IsaBellaBortoleto/AirDrums/Fotos/WhatsApp Image 2025-02-23 at 17.46.49 (1).jpeg

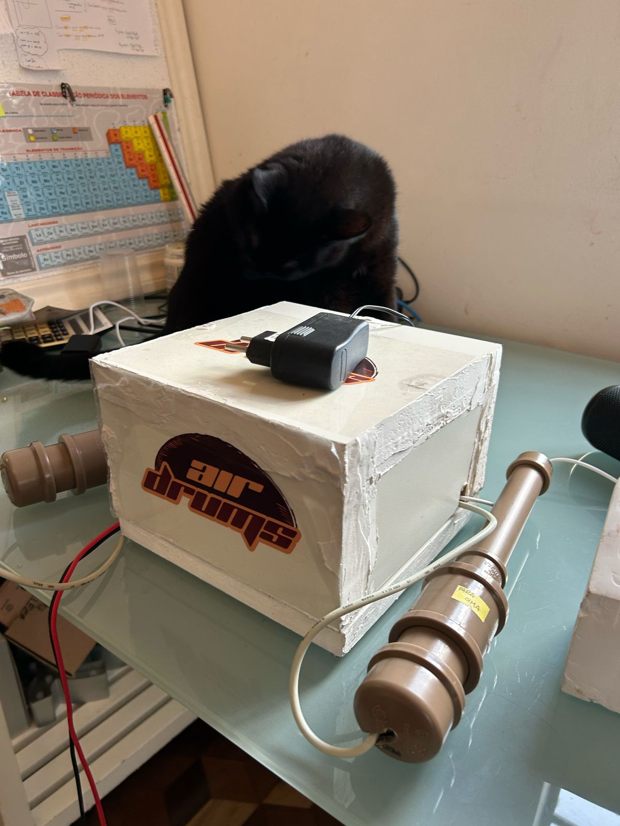
Fotos/WhatsApp Image 2025-02-23 at 17.46.49 (1).jpeg
