IsaBellaBortoleto/AirDrums/Vetores/diagrama_pretoebranco.png

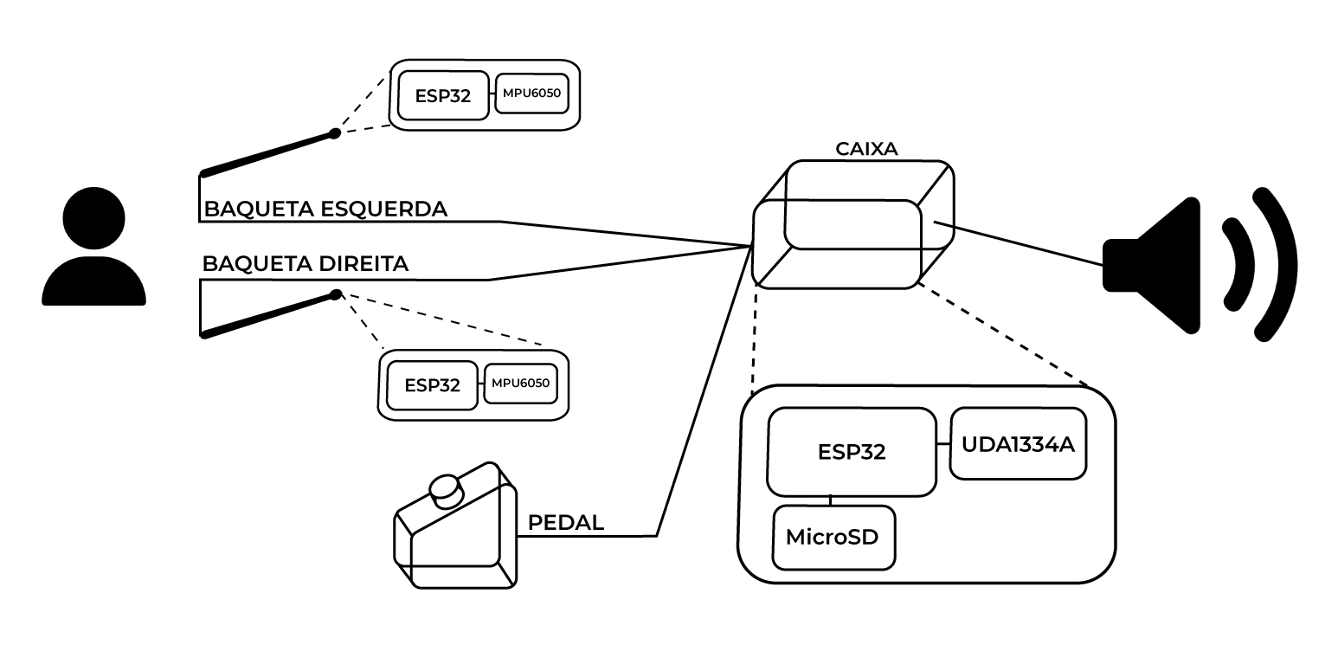
Vetores/diagrama_pretoebranco.png
