IsaBellaBortoleto/AirDrums/Vetores/MapaPratos.png

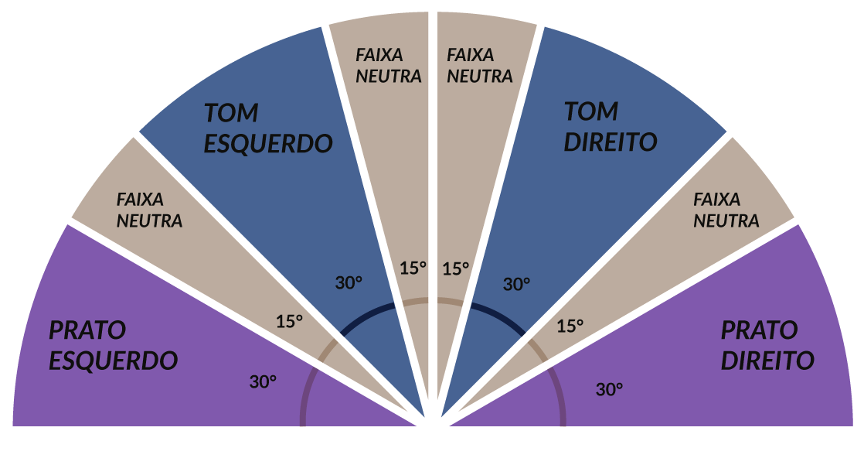
Vetores/MapaPratos.png
